MOSH-Insa-Toulouse/2025-2026-4GP_Shihadeh_Gleyzes/Kicad/Photo pour Github/Schematique.png

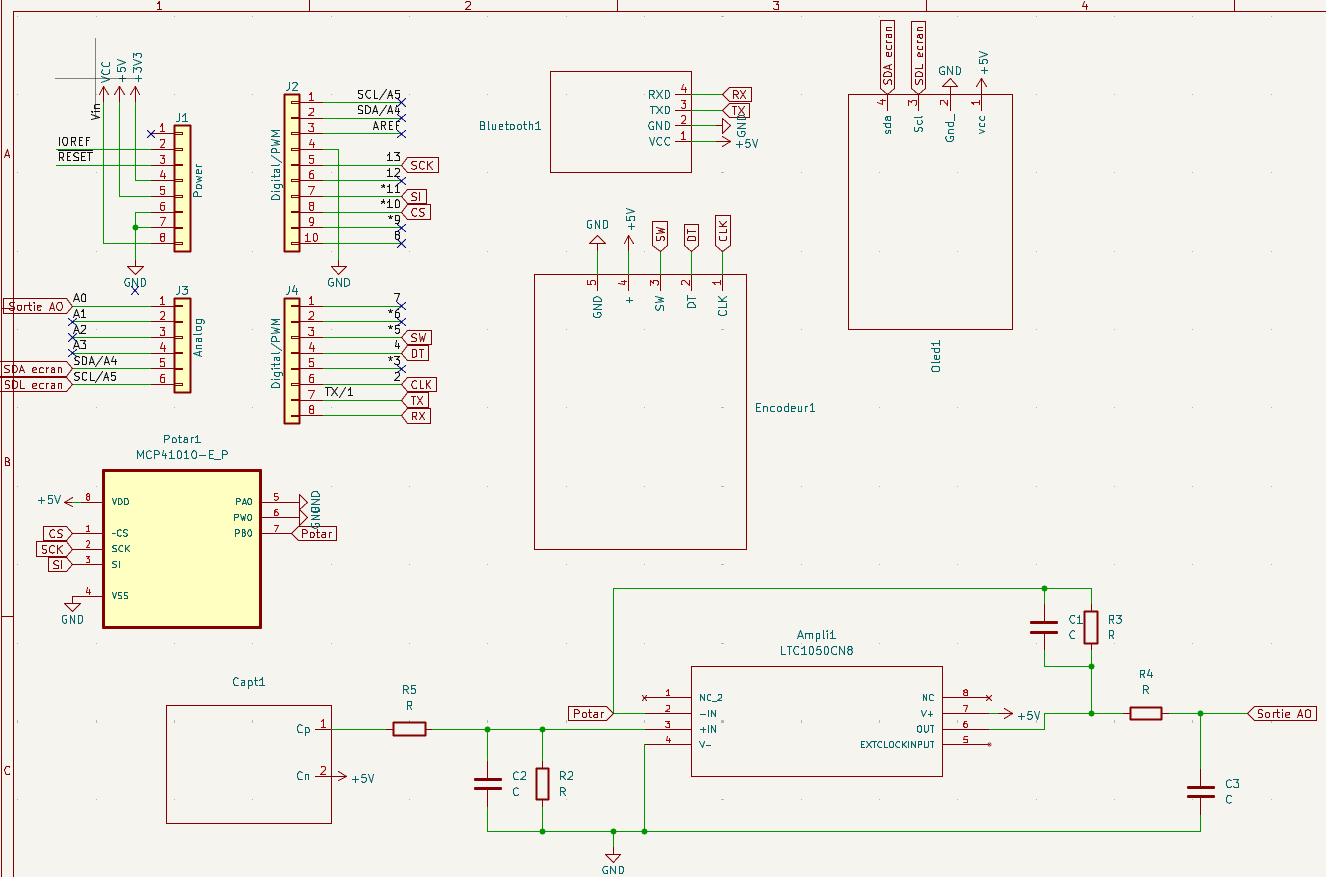
Kicad/Photo pour Github/Schematique.png
