MOSH-Insa-Toulouse/2025-2026-4GP_Shihadeh_Gleyzes/LTSpice/projet_symbol.asc

C1: cap; 100n
C2: cap; 100µ
C3: cap; 100n
C4: cap; 1p
R1: res; 1K
R2: res; 100k
R3: res; 1k
R4: res; 100k
R5: res; 10k
U1: LTC1050
V1: voltage; 5
V2: voltage; PULSE(0 1 0.2 0.1 0.1 2)
V3: voltage; SINE(0 325 50)
X1: symbole
Named nets: 0, ADC
.tran 5
;ac dec 100 1 1G
.param G0 10n
.param G1 10n
.param r1 100k
