MOSH-Insa-Toulouse/2025-2026-4GP_Shihadeh_Gleyzes/LTSpice/symbole.asc

B1: bi; I=V(cp,cn)*(10n+v(gc,gn)*10n)
C1: cap; 200µ
R1: res; 1k
Named nets: cn, cp, gn, gp, gc
